rweather/microbee-restoration/ROMs/character-set.png

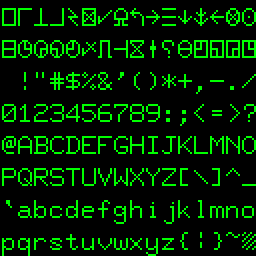
ROMs/character-set.png
