rweather/microbee-restoration/schematics/Microbee_Kit_Core_Board/ram_bank_1.kicad_sch

## KiCad design schematics/Microbee_Kit_Core_Board/ram_bank_1.kicad_sch (2024-03-17, an earlier design)

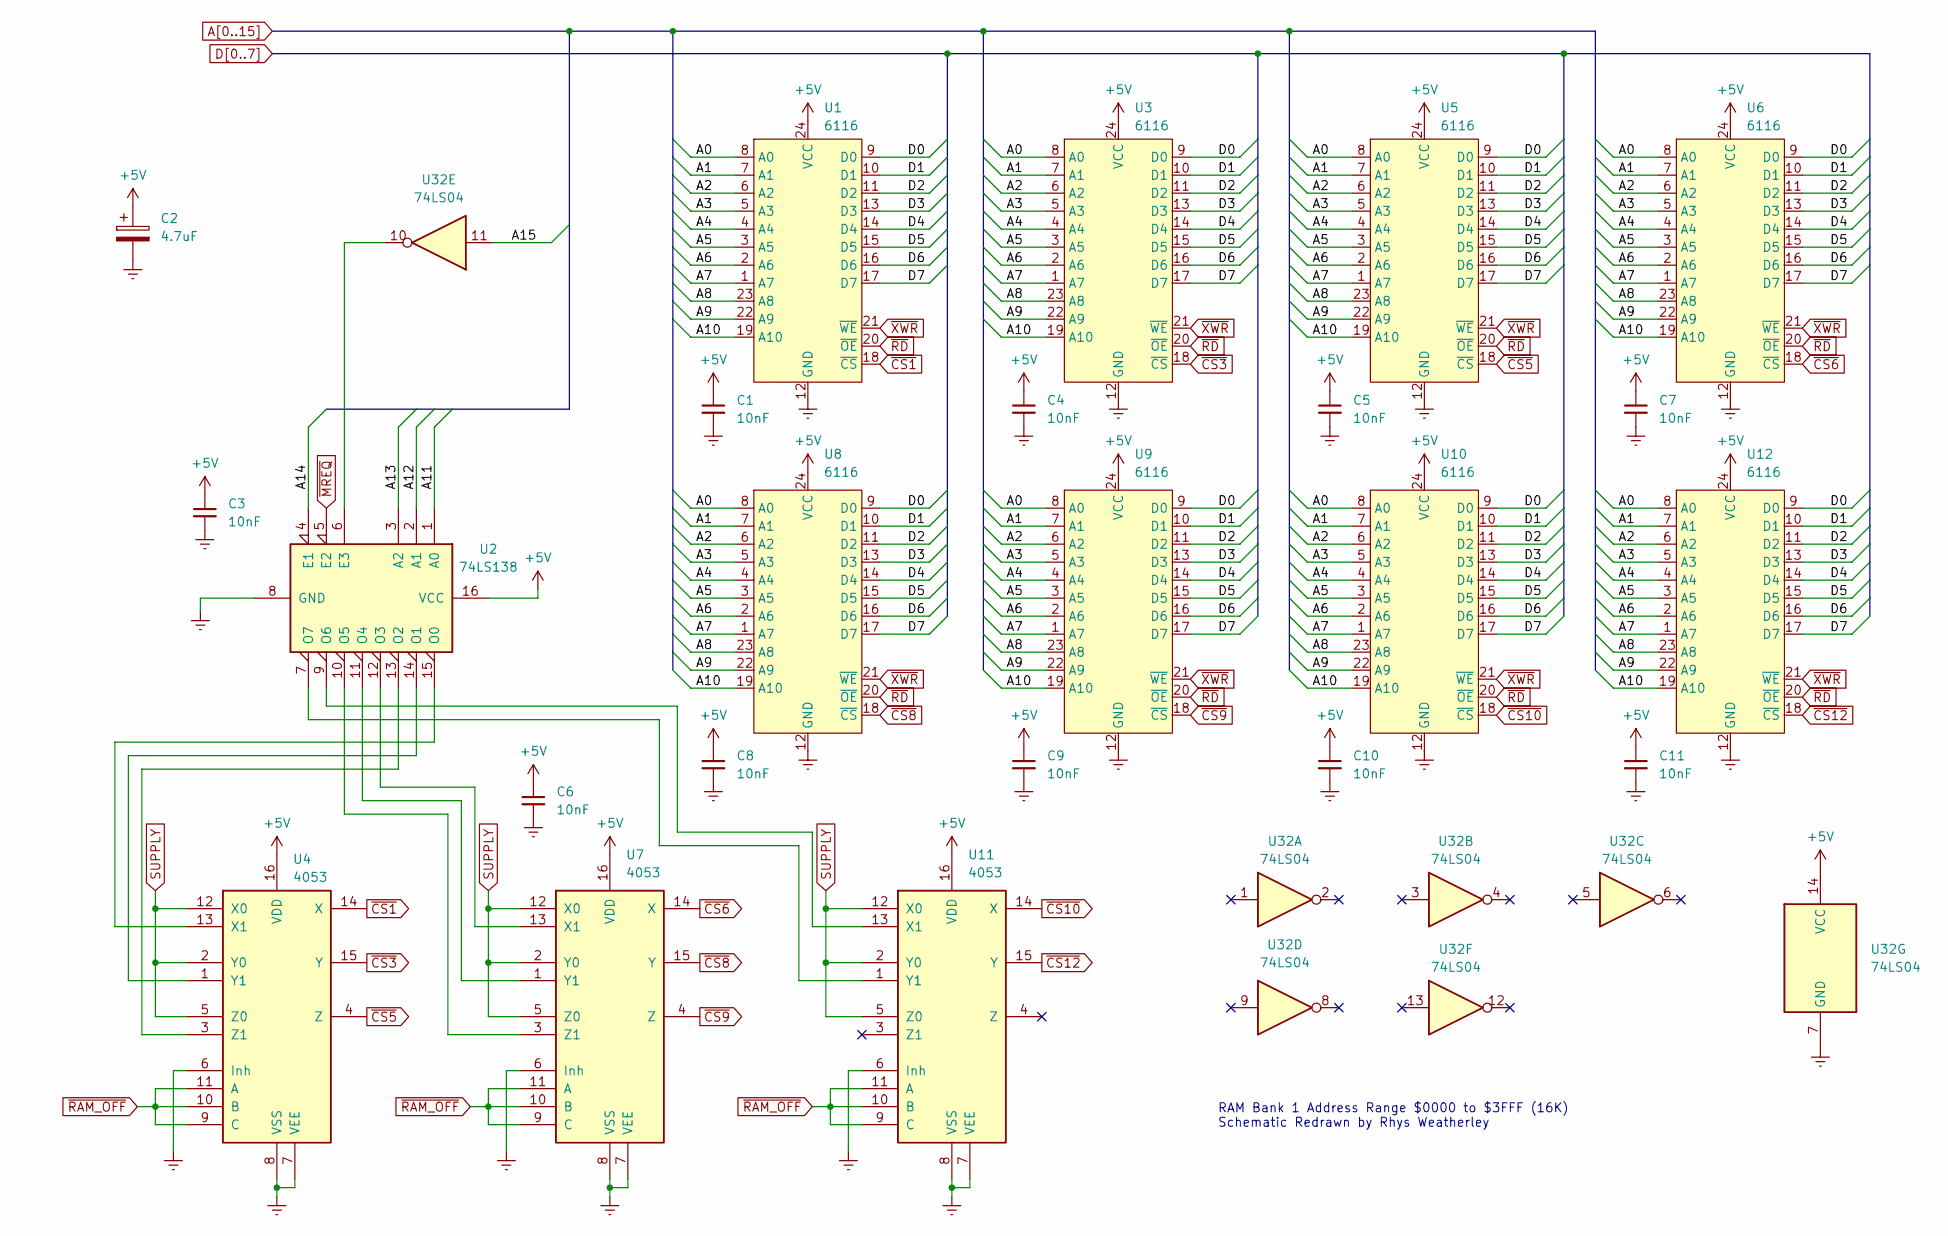
[picture p28: schematic ram_bank_1.kicad_sch]

Parts:
C1, C3, C4, C5, C6, C7, C8, C9, C10, C11: 10nF
C2: 4.7uF
U1, U3, U5, U6, U8, U9, U10, U12: 6116; DIP-24_W15.24mm
U2: 74LS138
U4, U7, U11: 4053
U32: 74LS04

Connections:
+5V: C1.1, C2.1, C3.1, C4.1, C5.1, C6.1, C7.1, C8.1, C9.1, C10.1, C11.1, U1.24 (VCC), U2.16 (VCC), U3.24 (VCC), U4.16 (VDD), U5.24 (VCC), U6.24 (VCC), U7.16 (VDD), U8.24 (VCC), U9.24 (VCC), U10.24 (VCC), U11.16 (VDD), U12.24 (VCC), U32.14 (VCC)
A0: U1.8 (A0), U3.8 (A0), U5.8 (A0), U6.8 (A0), U8.8 (A0), U9.8 (A0), U10.8 (A0), U12.8 (A0)
A1: U1.7 (A1), U3.7 (A1), U5.7 (A1), U6.7 (A1), U8.7 (A1), U9.7 (A1), U10.7 (A1), U12.7 (A1)
A2: U1.6 (A2), U3.6 (A2), U5.6 (A2), U6.6 (A2), U8.6 (A2), U9.6 (A2), U10.6 (A2), U12.6 (A2)
A3: U1.5 (A3), U3.5 (A3), U5.5 (A3), U6.5 (A3), U8.5 (A3), U9.5 (A3), U10.5 (A3), U12.5 (A3)
A4: U1.4 (A4), U3.4 (A4), U5.4 (A4), U6.4 (A4), U8.4 (A4), U9.4 (A4), U10.4 (A4), U12.4 (A4)
A5: U1.3 (A5), U3.3 (A5), U5.3 (A5), U6.3 (A5), U8.3 (A5), U9.3 (A5), U10.3 (A5), U12.3 (A5)
A6: U1.2 (A6), U3.2 (A6), U5.2 (A6), U6.2 (A6), U8.2 (A6), U9.2 (A6), U10.2 (A6), U12.2 (A6)
A7: U1.1 (A7), U3.1 (A7), U5.1 (A7), U6.1 (A7), U8.1 (A7), U9.1 (A7), U10.1 (A7), U12.1 (A7)
A8: U1.23 (A8), U3.23 (A8), U5.23 (A8), U6.23 (A8), U8.23 (A8), U9.23 (A8), U10.23 (A8), U12.23 (A8)
A9: U1.22 (A9), U3.22 (A9), U5.22 (A9), U6.22 (A9), U8.22 (A9), U9.22 (A9), U10.22 (A9), U12.22 (A9)
A10: U1.19 (A10), U3.19 (A10), U5.19 (A10), U6.19 (A10), U8.19 (A10), U9.19 (A10), U10.19 (A10), U12.19 (A10)
A11: U2.1 (A0)
A12: U2.2 (A1)
A13: U2.3 (A2)
A14: U2.4 (E1)
A15: U32.11
D0: U1.9 (D0), U3.9 (D0), U5.9 (D0), U6.9 (D0), U8.9 (D0), U9.9 (D0), U10.9 (D0), U12.9 (D0)
D1: U1.10 (D1), U3.10 (D1), U5.10 (D1), U6.10 (D1), U8.10 (D1), U9.10 (D1), U10.10 (D1), U12.10 (D1)
D2: U1.11 (D2), U3.11 (D2), U5.11 (D2), U6.11 (D2), U8.11 (D2), U9.11 (D2), U10.11 (D2), U12.11 (D2)
D3: U1.13 (D3), U3.13 (D3), U5.13 (D3), U6.13 (D3), U8.13 (D3), U9.13 (D3), U10.13 (D3), U12.13 (D3)
D4: U1.14 (D4), U3.14 (D4), U5.14 (D4), U6.14 (D4), U8.14 (D4), U9.14 (D4), U10.14 (D4), U12.14 (D4)
D5: U1.15 (D5), U3.15 (D5), U5.15 (D5), U6.15 (D5), U8.15 (D5), U9.15 (D5), U10.15 (D5), U12.15 (D5)
D6: U1.16 (D6), U3.16 (D6), U5.16 (D6), U6.16 (D6), U8.16 (D6), U9.16 (D6), U10.16 (D6), U12.16 (D6)
D7: U1.17 (D7), U3.17 (D7), U5.17 (D7), U6.17 (D7), U8.17 (D7), U9.17 (D7), U10.17 (D7), U12.17 (D7)
Earth: C1.2, C2.2, C3.2, C4.2, C5.2, C6.2, C7.2, C8.2, C9.2, C10.2, C11.2, U1.12 (GND), U2.8 (GND), U3.12 (GND), U4.6 (Inh), U4.7 (VEE), U4.8 (VSS), U5.12 (GND), U6.12 (GND), U7.6 (Inh), U7.7 (VEE), U7.8 (VSS), U8.12 (GND), U9.12 (GND), U10.12 (GND), U11.6 (Inh), U11.7 (VEE), U11.8 (VSS), U12.12 (GND), U32.7 (GND)
unnamed: U2.6 (E3), U32.10
unnamed: U2.10 (O5), U7.3 (Z1)
unnamed: U2.11 (O4), U7.1 (Y1)
unnamed: U2.12 (O3), U7.13 (X1)
unnamed: U2.13 (O2), U4.3 (Z1)
unnamed: U2.14 (O1), U4.1 (Y1)
unnamed: U2.15 (O0), U4.13 (X1)
unnamed: U2.7 (O7), U11.1 (Y1)
unnamed: U2.9 (O6), U11.13 (X1)
SUPPLY: U4.2 (Y0), U4.5 (Z0), U4.12 (X0), U7.2 (Y0), U7.5 (Z0), U7.12 (X0), U11.2 (Y0), U11.5 (Z0), U11.12 (X0)
~CS1: U1.18 (~CS), U4.14 (X)
~CS3: U3.18 (~CS), U4.15 (Y)
~CS5: U4.4 (Z), U5.18 (~CS)
~CS6: U6.18 (~CS), U7.14 (X)
~CS8: U7.15 (Y), U8.18 (~CS)
~CS9: U7.4 (Z), U9.18 (~CS)
~CS10: U10.18 (~CS), U11.14 (X)
~CS12: U11.15 (Y), U12.18 (~CS)
~MREQ: U2.5 (E2)
~RAM_OFF: U4.9 (C), U4.10 (B), U4.11 (A), U7.9 (C), U7.10 (B), U7.11 (A), U11.9 (C), U11.10 (B), U11.11 (A)
~RD: U1.20 (~OE), U3.20 (~OE), U5.20 (~OE), U6.20 (~OE), U8.20 (~OE), U9.20 (~OE), U10.20 (~OE), U12.20 (~OE)
~XWR: U1.21 (~WE), U3.21 (~WE), U5.21 (~WE), U6.21 (~WE), U8.21 (~WE), U9.21 (~WE), U10.21 (~WE), U12.21 (~WE)

Notes on the sheet:
RAM Bank 1 Address Range $0000 to $3FFF (16K) Schematic Redrawn by Rhys Weatherley
