rweather/microbee-restoration/schematics/Microbee_Kit_Core_Board/ram_bank_2.kicad_sch

## KiCad design schematics/Microbee_Kit_Core_Board/ram_bank_2.kicad_sch (2024-03-17, an earlier design)

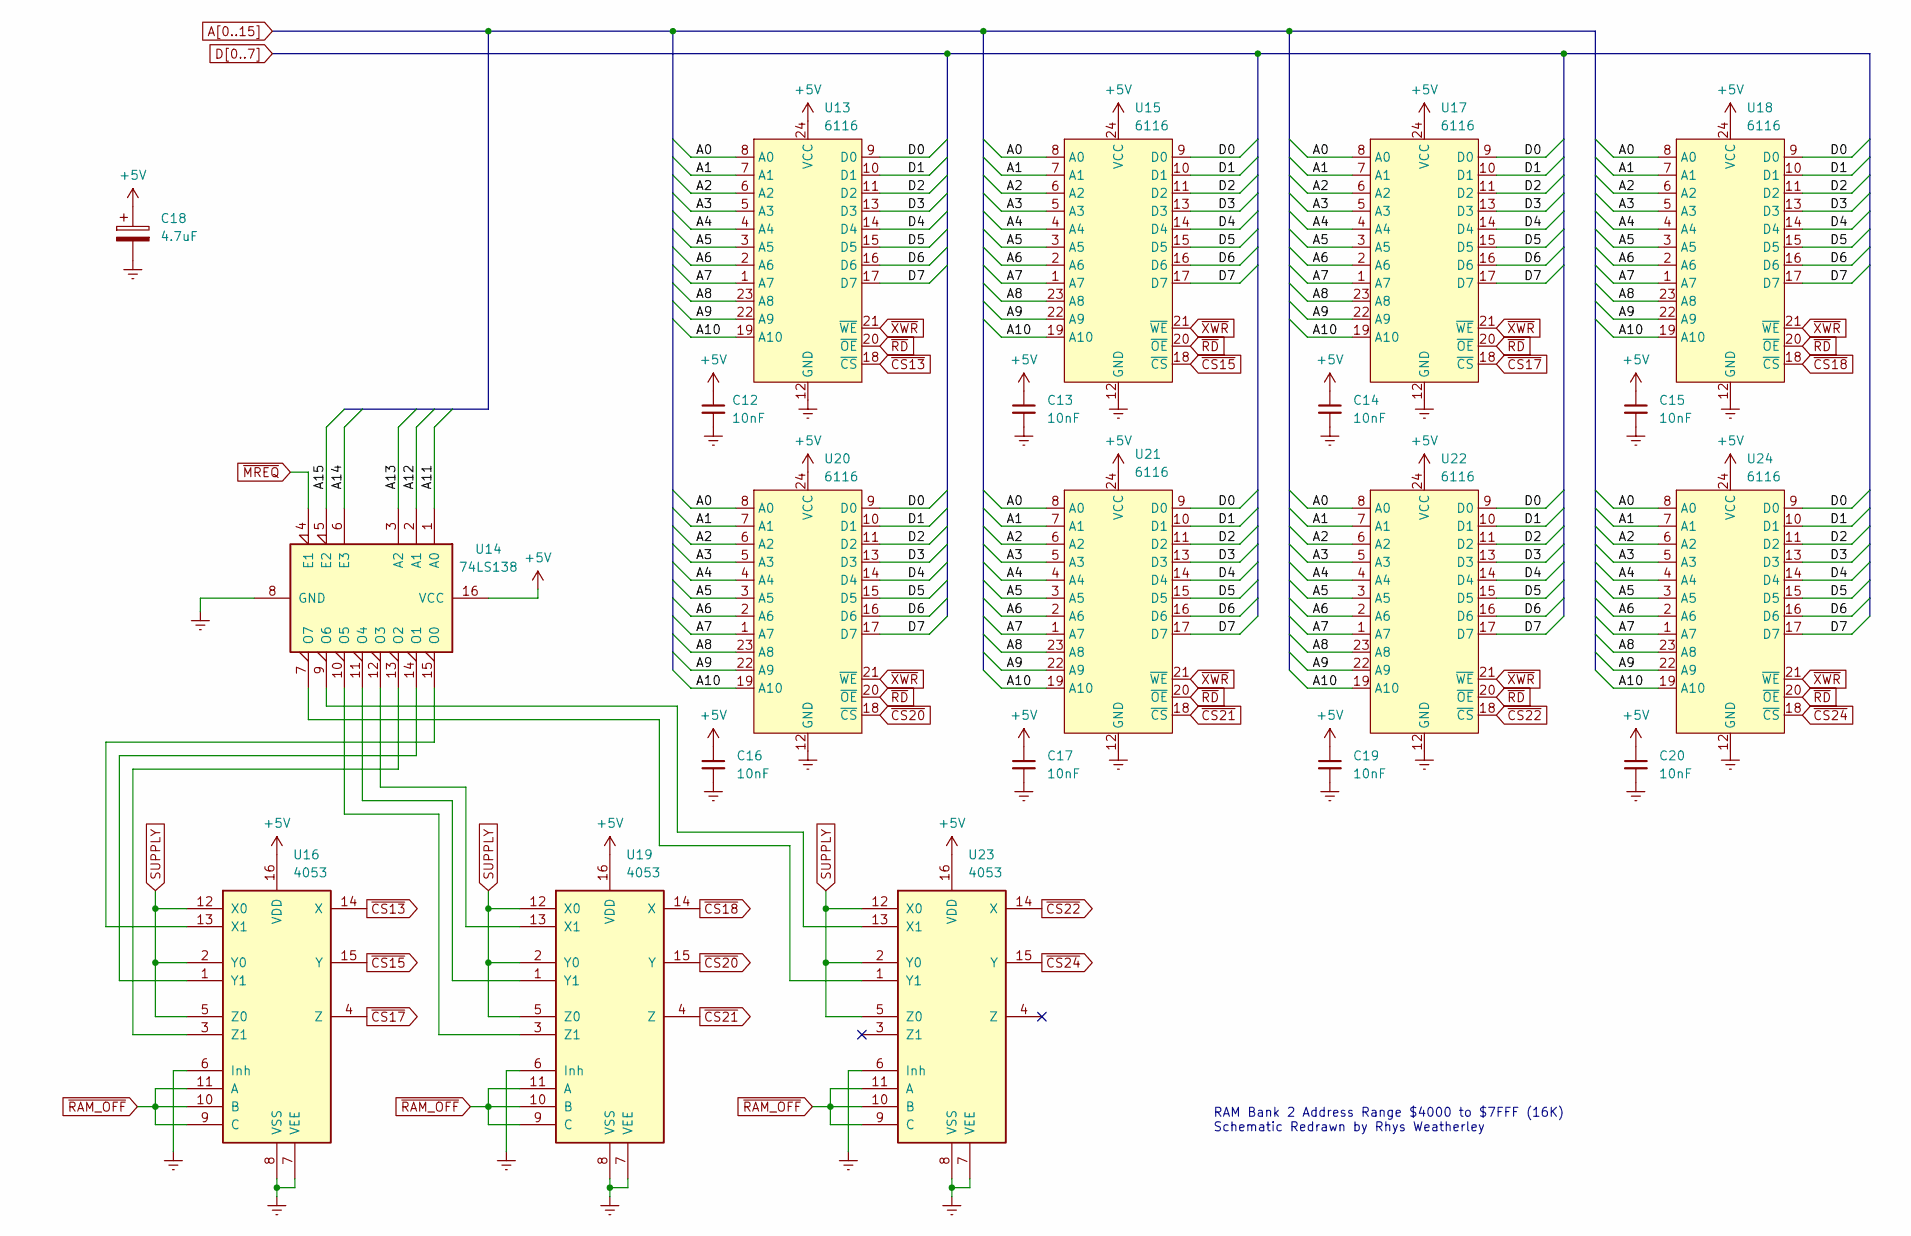
[picture p29: schematic ram_bank_2.kicad_sch]

Parts:
C12, C13, C14, C15, C16, C17, C19, C20: 10nF
C18: 4.7uF
U13, U15, U17, U18, U20, U21, U22, U24: 6116; DIP-24_W15.24mm
U14: 74LS138
U16, U19, U23: 4053

Connections:
+5V: C12.1, C13.1, C14.1, C15.1, C16.1, C17.1, C18.1, C19.1, C20.1, U13.24 (VCC), U14.16 (VCC), U15.24 (VCC), U16.16 (VDD), U17.24 (VCC), U18.24 (VCC), U19.16 (VDD), U20.24 (VCC), U21.24 (VCC), U22.24 (VCC), U23.16 (VDD), U24.24 (VCC)
A0: U13.8 (A0), U15.8 (A0), U17.8 (A0), U18.8 (A0), U20.8 (A0), U21.8 (A0), U22.8 (A0), U24.8 (A0)
A1: U13.7 (A1), U15.7 (A1), U17.7 (A1), U18.7 (A1), U20.7 (A1), U21.7 (A1), U22.7 (A1), U24.7 (A1)
A2: U13.6 (A2), U15.6 (A2), U17.6 (A2), U18.6 (A2), U20.6 (A2), U21.6 (A2), U22.6 (A2), U24.6 (A2)
A3: U13.5 (A3), U15.5 (A3), U17.5 (A3), U18.5 (A3), U20.5 (A3), U21.5 (A3), U22.5 (A3), U24.5 (A3)
A4: U13.4 (A4), U15.4 (A4), U17.4 (A4), U18.4 (A4), U20.4 (A4), U21.4 (A4), U22.4 (A4), U24.4 (A4)
A5: U13.3 (A5), U15.3 (A5), U17.3 (A5), U18.3 (A5), U20.3 (A5), U21.3 (A5), U22.3 (A5), U24.3 (A5)
A6: U13.2 (A6), U15.2 (A6), U17.2 (A6), U18.2 (A6), U20.2 (A6), U21.2 (A6), U22.2 (A6), U24.2 (A6)
A7: U13.1 (A7), U15.1 (A7), U17.1 (A7), U18.1 (A7), U20.1 (A7), U21.1 (A7), U22.1 (A7), U24.1 (A7)
A8: U13.23 (A8), U15.23 (A8), U17.23 (A8), U18.23 (A8), U20.23 (A8), U21.23 (A8), U22.23 (A8), U24.23 (A8)
A9: U13.22 (A9), U15.22 (A9), U17.22 (A9), U18.22 (A9), U20.22 (A9), U21.22 (A9), U22.22 (A9), U24.22 (A9)
A10: U13.19 (A10), U15.19 (A10), U17.19 (A10), U18.19 (A10), U20.19 (A10), U21.19 (A10), U22.19 (A10), U24.19 (A10)
A11: U14.1 (A0)
A12: U14.2 (A1)
A13: U14.3 (A2)
A14: U14.6 (E3)
A15: U14.5 (E2)
D0: U13.9 (D0), U15.9 (D0), U17.9 (D0), U18.9 (D0), U20.9 (D0), U21.9 (D0), U22.9 (D0), U24.9 (D0)
D1: U13.10 (D1), U15.10 (D1), U17.10 (D1), U18.10 (D1), U20.10 (D1), U21.10 (D1), U22.10 (D1), U24.10 (D1)
D2: U13.11 (D2), U15.11 (D2), U17.11 (D2), U18.11 (D2), U20.11 (D2), U21.11 (D2), U22.11 (D2), U24.11 (D2)
D3: U13.13 (D3), U15.13 (D3), U17.13 (D3), U18.13 (D3), U20.13 (D3), U21.13 (D3), U22.13 (D3), U24.13 (D3)
D4: U13.14 (D4), U15.14 (D4), U17.14 (D4), U18.14 (D4), U20.14 (D4), U21.14 (D4), U22.14 (D4), U24.14 (D4)
D5: U13.15 (D5), U15.15 (D5), U17.15 (D5), U18.15 (D5), U20.15 (D5), U21.15 (D5), U22.15 (D5), U24.15 (D5)
D6: U13.16 (D6), U15.16 (D6), U17.16 (D6), U18.16 (D6), U20.16 (D6), U21.16 (D6), U22.16 (D6), U24.16 (D6)
D7: U13.17 (D7), U15.17 (D7), U17.17 (D7), U18.17 (D7), U20.17 (D7), U21.17 (D7), U22.17 (D7), U24.17 (D7)
Earth: C12.2, C13.2, C14.2, C15.2, C16.2, C17.2, C18.2, C19.2, C20.2, U13.12 (GND), U14.8 (GND), U15.12 (GND), U16.6 (Inh), U16.7 (VEE), U16.8 (VSS), U17.12 (GND), U18.12 (GND), U19.6 (Inh), U19.7 (VEE), U19.8 (VSS), U20.12 (GND), U21.12 (GND), U22.12 (GND), U23.6 (Inh), U23.7 (VEE), U23.8 (VSS), U24.12 (GND)
unnamed: U14.7 (O7), U23.1 (Y1)
unnamed: U14.9 (O6), U23.13 (X1)
unnamed: U14.10 (O5), U19.3 (Z1)
unnamed: U14.11 (O4), U19.1 (Y1)
unnamed: U14.12 (O3), U19.13 (X1)
unnamed: U14.13 (O2), U16.3 (Z1)
unnamed: U14.14 (O1), U16.1 (Y1)
unnamed: U14.15 (O0), U16.13 (X1)
SUPPLY: U16.2 (Y0), U16.5 (Z0), U16.12 (X0), U19.2 (Y0), U19.5 (Z0), U19.12 (X0), U23.2 (Y0), U23.5 (Z0), U23.12 (X0)
~CS13: U13.18 (~CS), U16.14 (X)
~CS15: U15.18 (~CS), U16.15 (Y)
~CS17: U16.4 (Z), U17.18 (~CS)
~CS18: U18.18 (~CS), U19.14 (X)
~CS20: U19.15 (Y), U20.18 (~CS)
~CS21: U19.4 (Z), U21.18 (~CS)
~CS22: U22.18 (~CS), U23.14 (X)
~CS24: U23.15 (Y), U24.18 (~CS)
~MREQ: U14.4 (E1)
~RAM_OFF: U16.9 (C), U16.10 (B), U16.11 (A), U19.9 (C), U19.10 (B), U19.11 (A), U23.9 (C), U23.10 (B), U23.11 (A)
~RD: U13.20 (~OE), U15.20 (~OE), U17.20 (~OE), U18.20 (~OE), U20.20 (~OE), U21.20 (~OE), U22.20 (~OE), U24.20 (~OE)
~XWR: U13.21 (~WE), U15.21 (~WE), U17.21 (~WE), U18.21 (~WE), U20.21 (~WE), U21.21 (~WE), U22.21 (~WE), U24.21 (~WE)

Notes on the sheet:
RAM Bank 2 Address Range $4000 to $7FFF (16K) Schematic Redrawn by Rhys Weatherley
