rweather/microbee-restoration/schematics/Microbee_Kit_Main_Board/io_ports.kicad_sch

## KiCad design schematics/Microbee_Kit_Main_Board/io_ports.kicad_sch (2024-02-11)

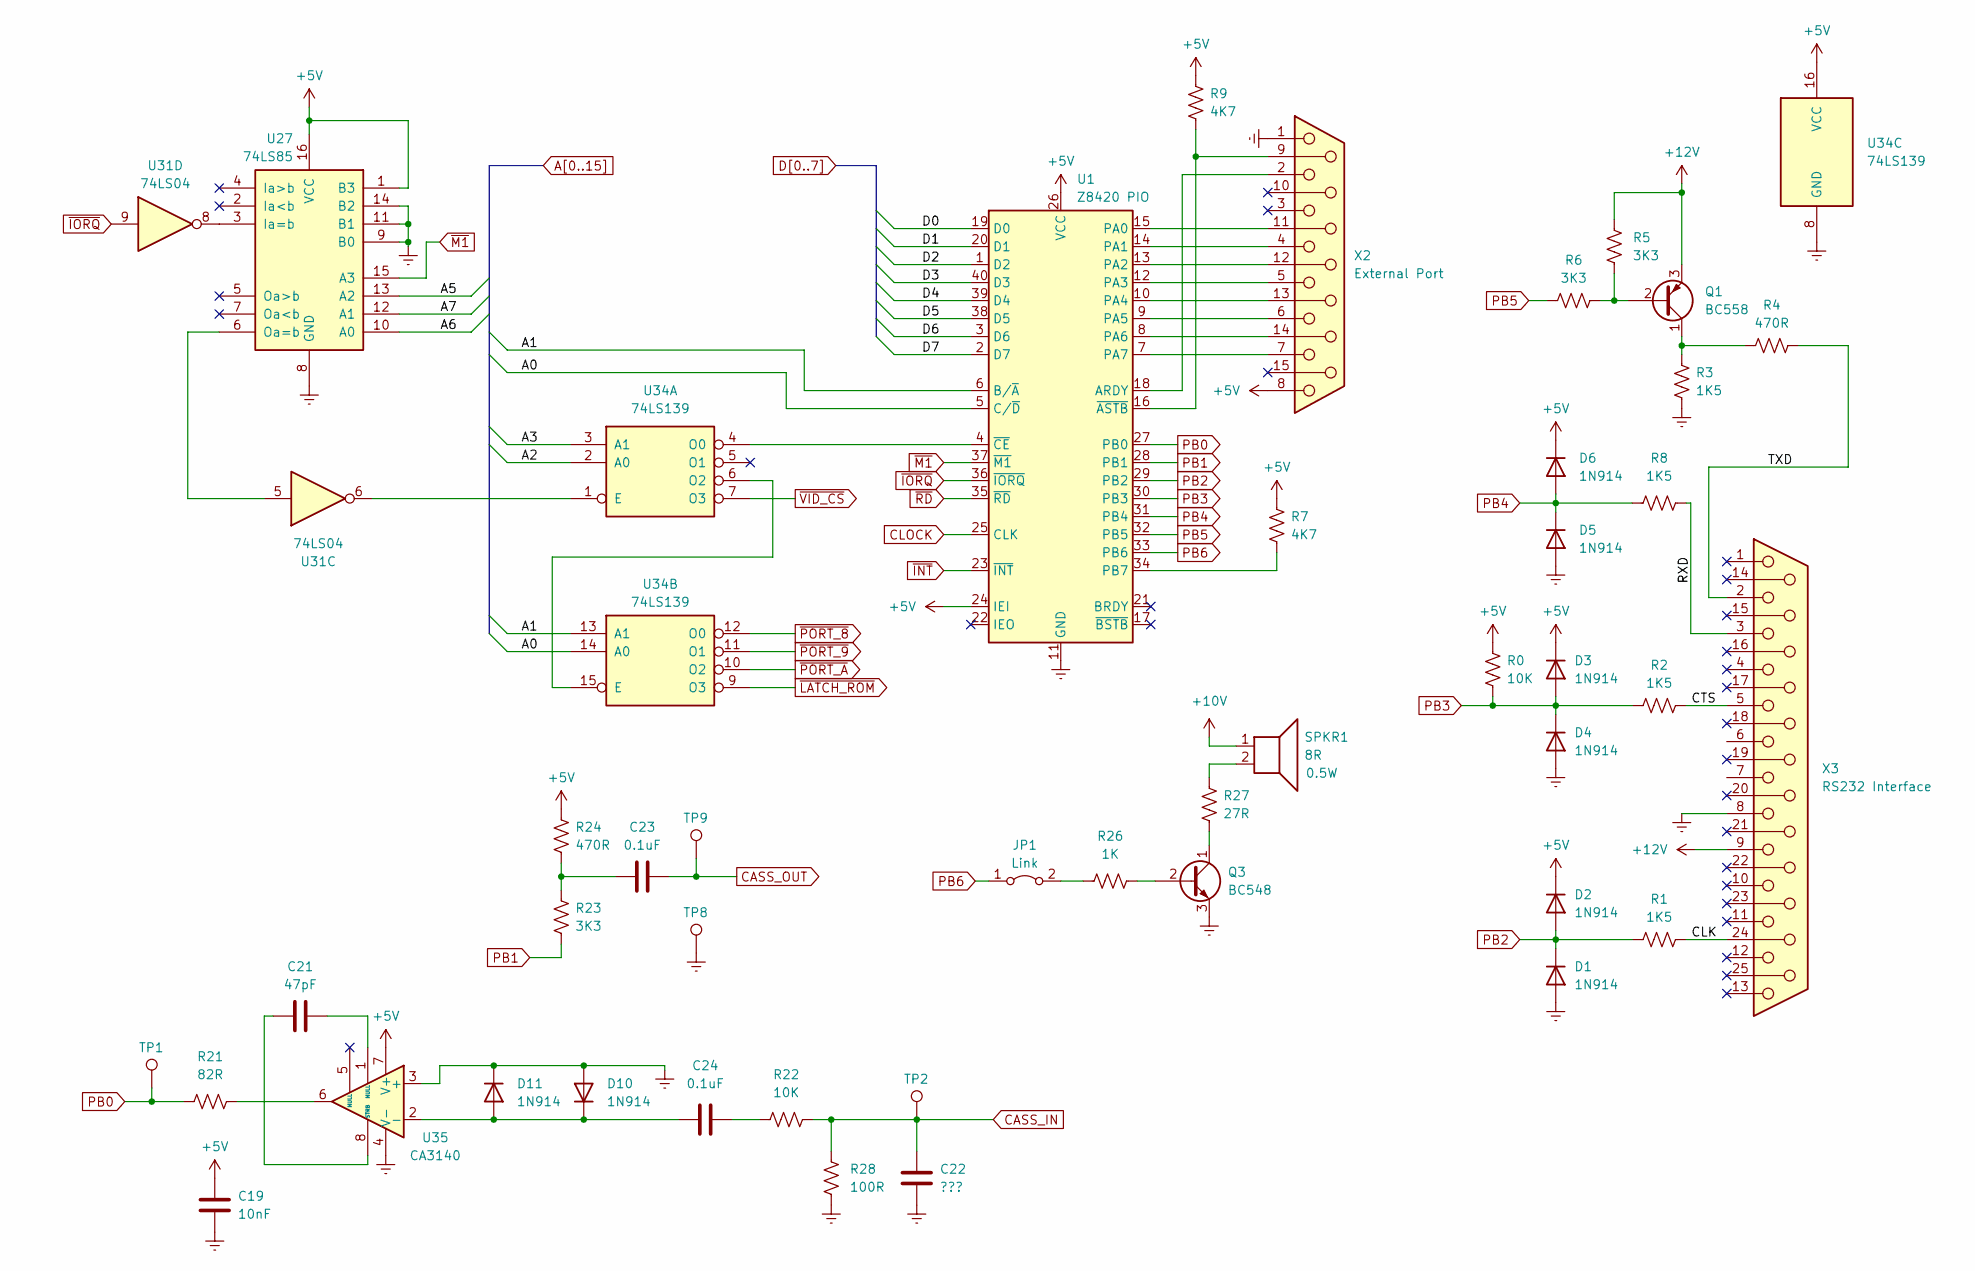
[picture p35: schematic io_ports.kicad_sch]

Parts:
C19: 10nF
C21: 47pF
C22: ???
C23, C24: 0.1uF
D1, D2, D3, D4, D5, D6, D10, D11: 1N914; D_DO-35_SOD27_P7.62mm_Horizontal
JP1: Link
Q1: BC558; TO-92_Inline
Q3: BC548; TO-92_Inline
R0, R22: 10K; R_Axial_DIN0207_L6.3mm_D2.5mm_P7.62mm_Horizontal
R1, R2, R3, R8: 1K5; R_Axial_DIN0207_L6.3mm_D2.5mm_P7.62mm_Horizontal
R4, R24: 470R; R_Axial_DIN0207_L6.3mm_D2.5mm_P7.62mm_Horizontal
R5, R6, R23: 3K3; R_Axial_DIN0207_L6.3mm_D2.5mm_P7.62mm_Horizontal
R7, R9: 4K7; R_Axial_DIN0207_L6.3mm_D2.5mm_P7.62mm_Horizontal
R21: 82R; R_Axial_DIN0207_L6.3mm_D2.5mm_P7.62mm_Horizontal
R26: 1K; R_Axial_DIN0207_L6.3mm_D2.5mm_P7.62mm_Horizontal
R27: 27R; R_Axial_DIN0207_L6.3mm_D2.5mm_P7.62mm_Horizontal
R28: 100R; R_Axial_DIN0207_L6.3mm_D2.5mm_P7.62mm_Horizontal
SPKR1: 8R
TP1, TP2, TP8, TP9: TestPoint
U1: Z8420 PIO; DIP-40_W15.24mm
U27: 74LS85; DIP-16_W7.62mm
U31: 74LS04
U34: 74LS139; DIP-16_W7.62mm
U35: CA3140; DIP-8-16_W7.62mm
X2: External Port; DSUB-15_Female_Horizontal_P2.77x2.84mm_EdgePinOffset9.40mm
X3: RS232 Interface; DSUB-37_Female_Horizontal_P2.77x2.54mm_EdgePinOffset9.40mm

Connections:
+5V: C19.1, D2.1 (K), D3.1 (K), D6.1 (K), R0.1, R7.1, R9.1, R24.1, U1.24 (IEI), U1.26 (VCC), U27.1 (B3), U27.16 (VCC), U34.16 (VCC), U35.7 (V+), X2.8
+10V: SPKR1.1
+12V: Q1.3 (E), R5.1, X3.9
A0: U1.5 (C/~D), U34.14 (A0)
A1: U1.6 (B/~A), U34.13 (A1)
A2: U34.2 (A0)
A3: U34.3 (A1)
A5: U27.13 (A2)
A6: U27.10 (A0)
A7: U27.12 (A1)
CASS_IN: C22.1, R22.2, R28.1, TP2.1
CASS_OUT: C23.2, TP9.1
CLK: R1.2, X3.24
CLOCK: U1.25 (CLK)
CTS: R2.2, X3.5
D0: U1.19 (D0)
D1: U1.20 (D1)
D2: U1.1 (D2)
D3: U1.40 (D3)
D4: U1.39 (D4)
D5: U1.38 (D5)
D6: U1.3 (D6)
D7: U1.2 (D7)
Earth: C19.2, C22.2, D1.2 (A), D4.2 (A), D5.2 (A), D10.2 (A), D11.1 (K), Q3.3 (E), R3.2, R28.2, TP8.1, U1.11 (GND), U27.8 (GND), U27.9 (B0), U27.11 (B1), U27.14 (B2), U34.8 (GND), U35.3 (+), U35.4 (V-), X2.1, X3.8
unnamed: C21.1, U35.8 (STRB)
unnamed: C21.2, U35.1 (NULL)
unnamed: C23.1, R23.1, R24.2
unnamed: C24.1, D10.1 (K), D11.2 (A), U35.2 (-)
unnamed: C24.2, R22.1
unnamed: JP1.2 (B), R26.1
unnamed: Q1.1 (C), R3.1, R4.1
unnamed: Q1.2 (B), R5.2, R6.2
unnamed: Q3.1 (C), R27.2
unnamed: Q3.2 (B), R26.2
unnamed: R7.2, U1.34 (PB7)
unnamed: R9.2, U1.16 (~ASTB), X2.9
unnamed: R21.2, U35.6
unnamed: R27.1, SPKR1.2
unnamed: U1.4 (~CE), U34.4 (O0)
unnamed: U1.7 (PA7), X2.7
unnamed: U1.8 (PA6), X2.14
unnamed: U1.9 (PA5), X2.6
unnamed: U1.10 (PA4), X2.13
unnamed: U1.12 (PA3), X2.5
unnamed: U1.13 (PA2), X2.12
unnamed: U1.14 (PA1), X2.4
unnamed: U1.15 (PA0), X2.11 (P111)
unnamed: U1.18 (ARDY), X2.2
unnamed: U27.3 (Ia=b), U31.8
unnamed: U27.6 (Oa=b), U31.5
unnamed: U31.6, U34.1 (E)
unnamed: U34.6 (O2), U34.15 (E)
PB0: R21.1, TP1.1, U1.27 (PB0)
PB1: R23.2, U1.28 (PB1)
PB2: D1.1 (K), D2.2 (A), R1.1, U1.29 (PB2)
PB3: D3.2 (A), D4.1 (K), R0.2, R2.1, U1.30 (PB3)
PB4: D5.1 (K), D6.2 (A), R8.1, U1.31 (PB4)
PB5: R6.1, U1.32 (PB5)
PB6: JP1.1 (A), U1.33 (PB6)
RXD: R8.2, X3.3
TXD: R4.2, X3.2
~INT: U1.23 (~INT)
~IORQ: U1.36 (~IORQ), U31.9
~LATCH_ROM: U34.9 (O3)
~M1: U1.37 (~M1), U27.15 (A3)
~PORT_8: U34.12 (O0)
~PORT_9: U34.11 (O1)
~PORT_A: U34.10 (O2)
~RD: U1.35 (~RD)
~VID_CS: U34.7 (O3)
