rweather/microbee-restoration/schematics/Microbee_Kit_Main_Board/video_controller.kicad_sch

## KiCad design schematics/Microbee_Kit_Main_Board/video_controller.kicad_sch (2024-03-17, an earlier design)

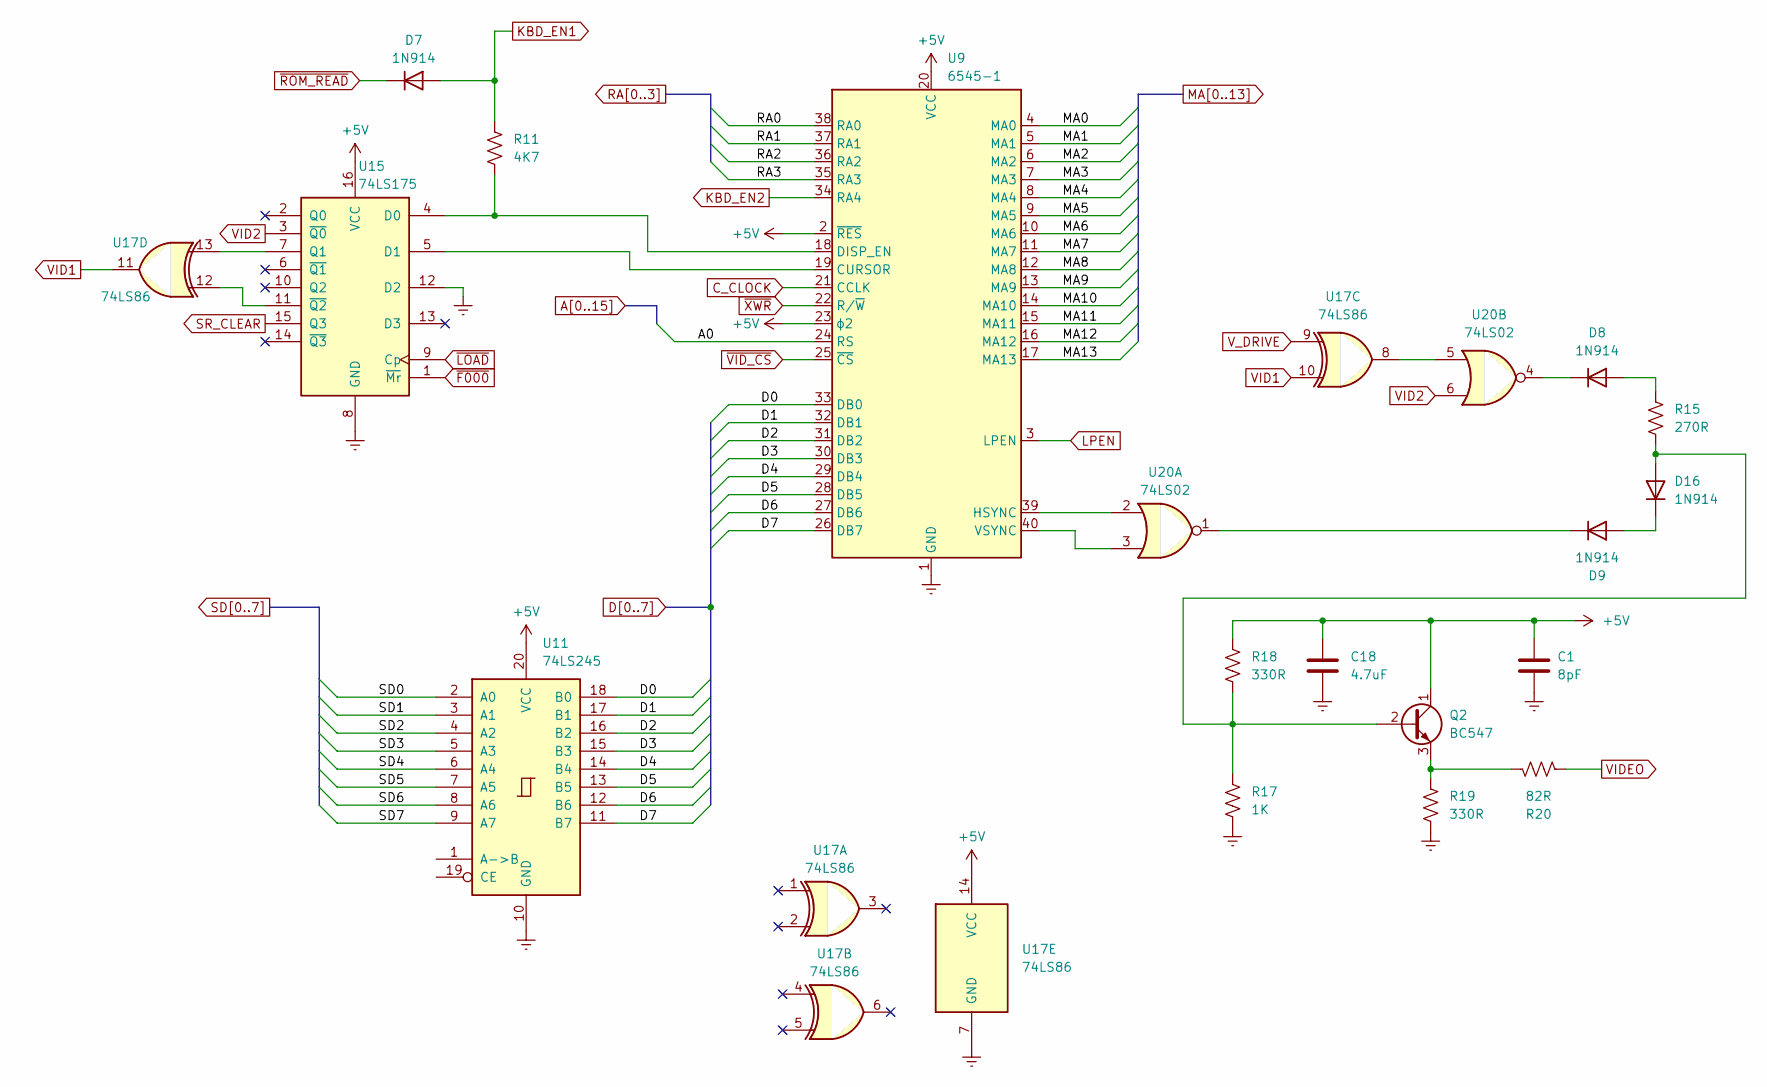
[picture p37: schematic video_controller.kicad_sch]

Parts:
C1: 8pF
C18: 4.7uF
D7, D8, D9, D16: 1N914; D_DO-35_SOD27_P7.62mm_Horizontal
Q2: BC547; TO-92_Inline
R11: 4K7; R_Axial_DIN0207_L6.3mm_D2.5mm_P7.62mm_Horizontal
R15: 270R; R_Axial_DIN0207_L6.3mm_D2.5mm_P7.62mm_Horizontal
R17: 1K; R_Axial_DIN0207_L6.3mm_D2.5mm_P7.62mm_Horizontal
R18, R19: 330R; R_Axial_DIN0207_L6.3mm_D2.5mm_P7.62mm_Horizontal
R20: 82R; R_Axial_DIN0207_L6.3mm_D2.5mm_P7.62mm_Horizontal
U9: 6545-1; DIP-40_W15.24mm
U11: 74LS245; DIP-20_W7.62mm
U15: 74LS175; DIP-16_W7.62mm
U17: 74LS86
U20: 74LS02

Connections:
+5V: C1.1, C18.1, Q2.1 (C), R18.1, U9.2 (~RES), U9.20 (VCC), U9.23 (ϕ2), U11.20 (VCC), U15.16 (VCC), U17.14 (VCC)
A0: U9.24 (RS)
C_CLOCK: U9.21 (CCLK)
D0: U9.33 (DB0), U11.18 (B0)
D1: U9.32 (DB1), U11.17 (B1)
D2: U9.31 (DB2), U11.16 (B2)
D3: U9.30 (DB3), U11.15 (B3)
D4: U9.29 (DB4), U11.14 (B4)
D5: U9.28 (DB5), U11.13 (B5)
D6: U9.27 (DB6), U11.12 (B6)
D7: U9.26 (DB7), U11.11 (B7)
Earth: C1.2, C18.2, R17.2, R19.2, U9.1 (GND), U11.10 (GND), U15.8 (GND), U15.12 (D2), U17.7 (GND)
KBD_EN1: D7.2 (A), R11.1
KBD_EN2: U9.34 (RA4)
LPEN: U9.3 (LPEN)
MA0: U9.4 (MA0)
MA1: U9.5 (MA1)
MA2: U9.6 (MA2)
MA3: U9.7 (MA3)
MA4: U9.8 (MA4)
MA5: U9.9 (MA5)
MA6: U9.10 (MA6)
MA7: U9.11 (MA7)
MA8: U9.12 (MA8)
MA9: U9.13 (MA9)
MA10: U9.14 (MA10)
MA11: U9.15 (MA11)
MA12: U9.16 (MA12)
MA13: U9.17 (MA13)
unnamed: D8.1 (K), U20.4
unnamed: D8.2 (A), R15.1
unnamed: D9.1 (K), U20.1
unnamed: D9.2 (A), D16.1 (K)
unnamed: D16.2 (A), Q2.2 (B), R15.2, R17.1, R18.2
unnamed: Q2.3 (E), R19.1, R20.1
unnamed: R11.2, U9.18 (DISP_EN), U15.4 (D0)
unnamed: U9.19 (CURSOR), U15.5 (D1)
unnamed: U15.7 (Q1), U17.13
unnamed: U15.11 (~Q2), U17.12
unnamed: U17.8, U20.5
unnamed: U9.39 (HSYNC), U20.2
unnamed: U9.40 (VSYNC), U20.3
RA0: U9.38 (RA0)
RA1: U9.37 (RA1)
RA2: U9.36 (RA2)
RA3: U9.35 (RA3)
SD0: U11.2 (A0)
SD1: U11.3 (A1)
SD2: U11.4 (A2)
SD3: U11.5 (A3)
SD4: U11.6 (A4)
SD5: U11.7 (A5)
SD6: U11.8 (A6)
SD7: U11.9 (A7)
SR_CLEAR: U15.15 (Q3)
VID1: U17.10, U17.11
VID2: U15.3 (~Q0), U20.6
VIDEO: R20.2
V_DRIVE: U17.9
~F000: U15.1 (~Mr)
~LOAD: U15.9 (Cp)
~ROM_READ: D7.1 (K)
~VID_CS: U9.25 (~CS)
~XWR: U9.22 (R/~W)
